voluta-coop/eGallinero/Images/_DSC0915.jpg

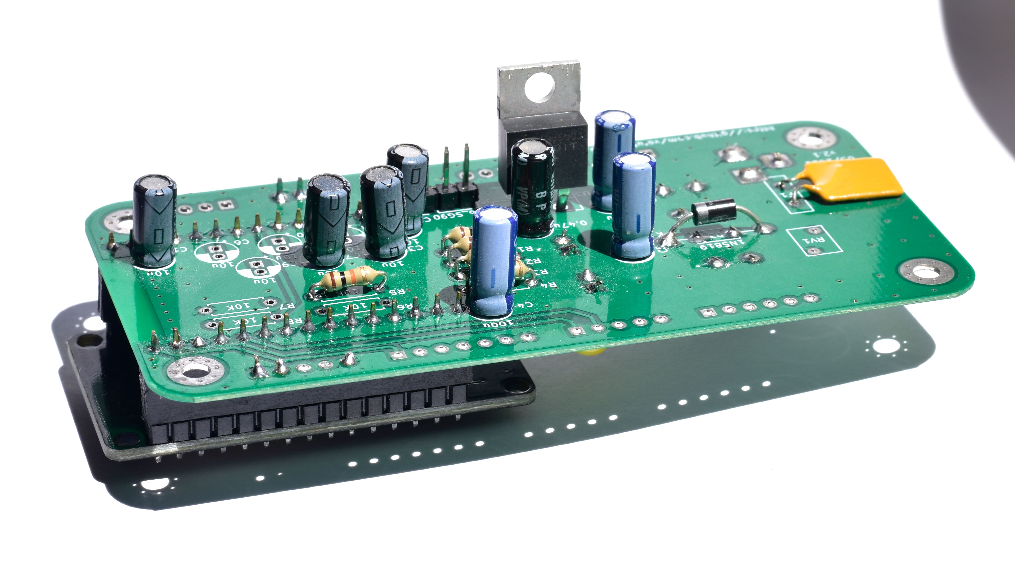
Images/_DSC0915.jpg
