voluta-coop/eGallinero/Images/_DSC0916.jpg

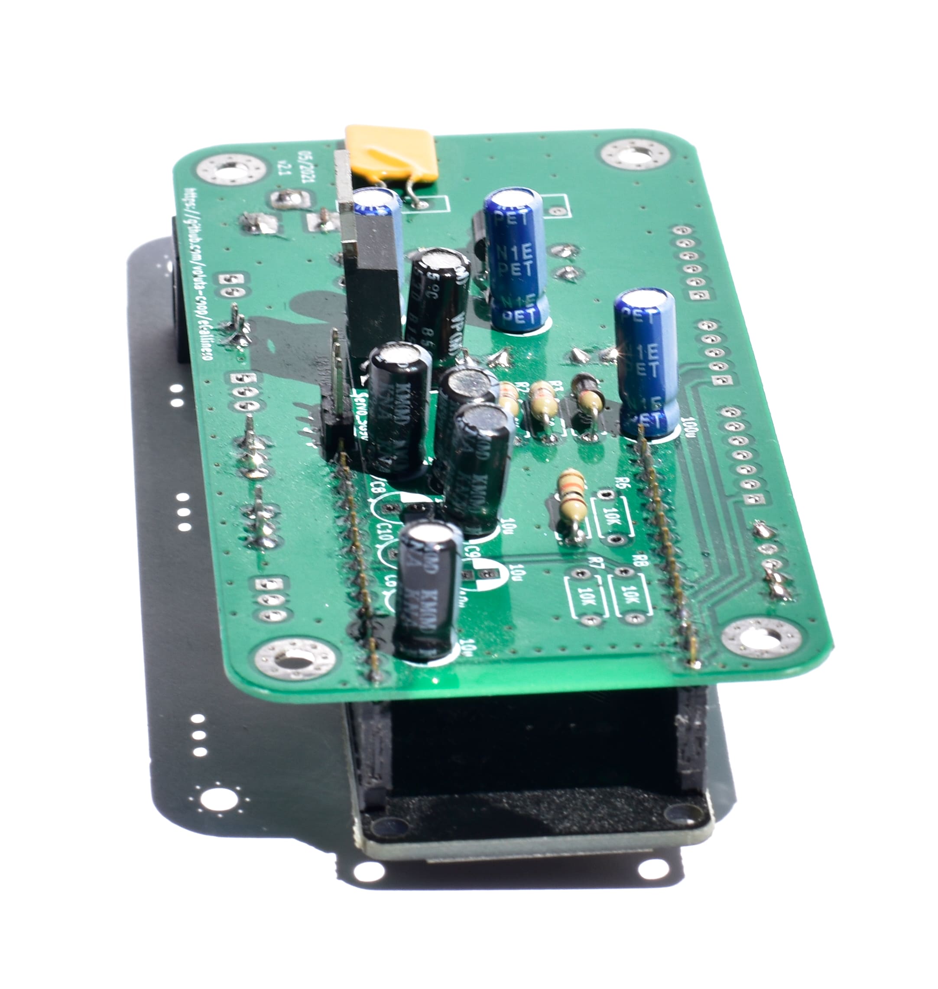
Images/_DSC0916.jpg
