voluta-coop/eGallinero/Images/_DSC0918.jpg

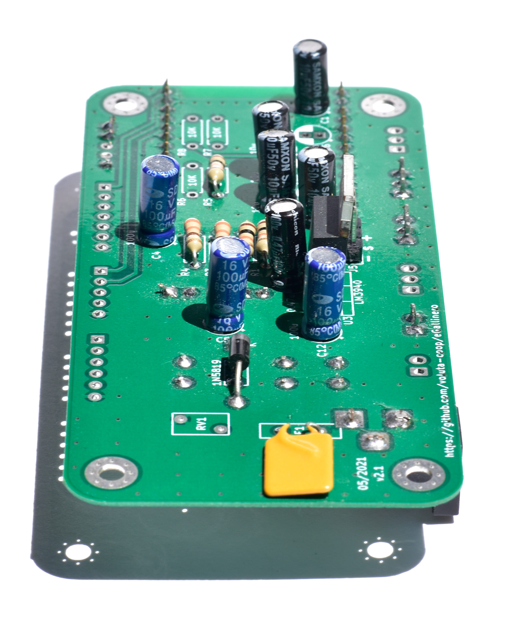
Images/_DSC0918.jpg
