voluta-coop/eGallinero/Images/_DSC0919.jpg

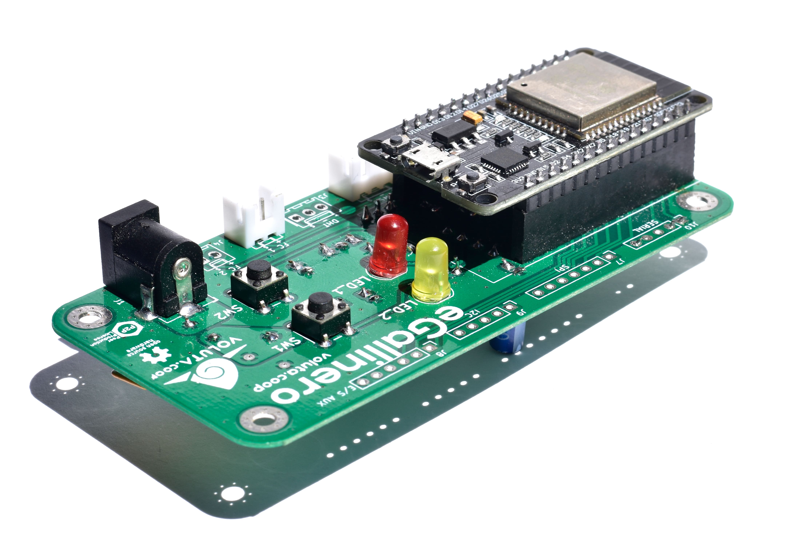
Images/_DSC0919.jpg
