voluta-coop/eGallinero/Images/_DSC0920.jpg

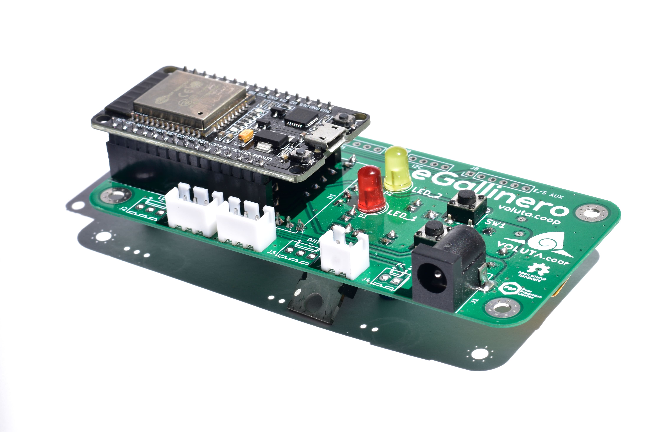
Images/_DSC0920.jpg
