voluta-coop/eGallinero/Images/_DSC0921.jpg

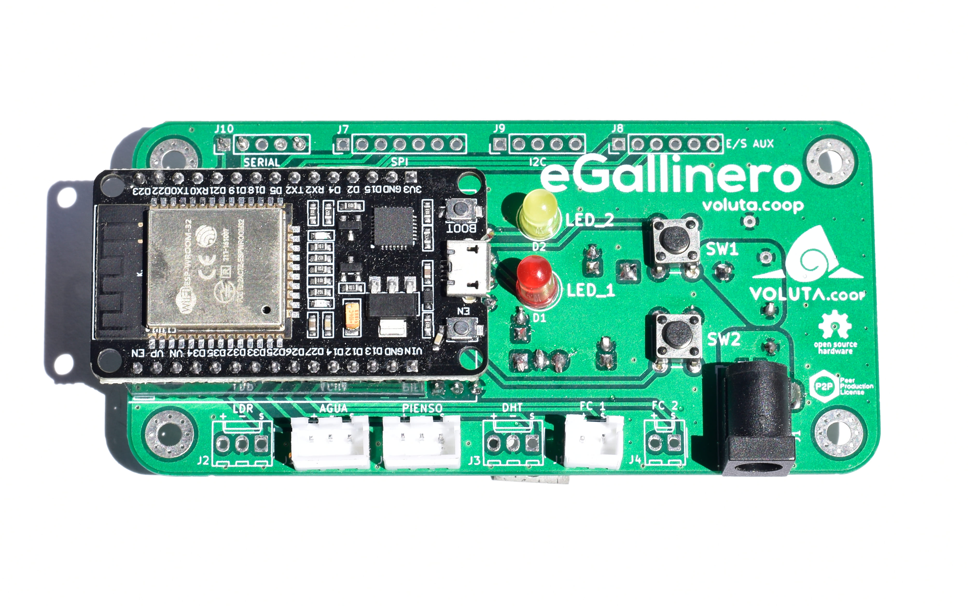
Images/_DSC0921.jpg
