voluta-coop/eGallinero/Images/eGallinero_BOTTOM.png

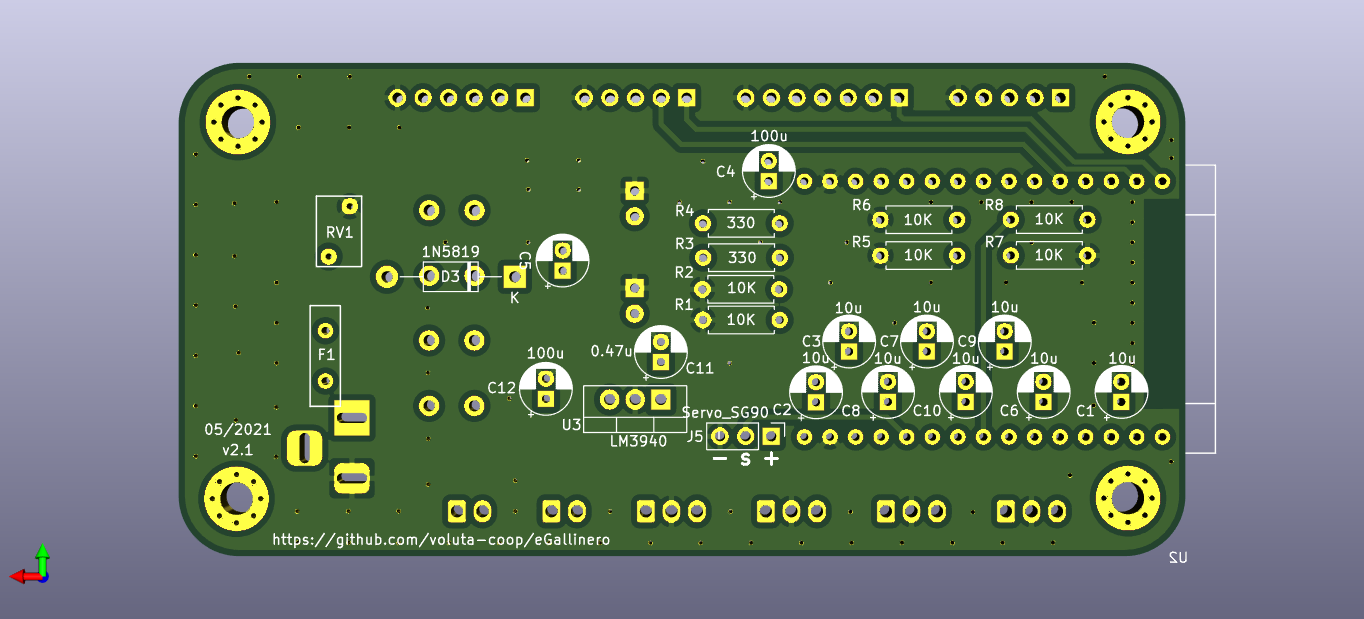
Images/eGallinero_BOTTOM.png
